CuriousTech/UT181A_WiFi/Arduino/jsonstring.h

// JSON string helper

class jsonString
{
public:
  jsonString(const char *pLabel = NULL)
  {
    m_cnt = 0;
    s = String("{");
    if(pLabel)
    {
      s += "\"cmd\":\"";
      s += pLabel, s += "\",";
    }
  }
        
  String Close(void)
  {
    s += "}";
    return s;
  }

  void Var(const char *key, int iVal)
  {
    if(m_cnt) s += ",";
    s += "\"";
    s += key;
    s += "\":";
    s += iVal;
    m_cnt++;
  }

  void Var(const char *key, uint32_t iVal)
  {
    if(m_cnt) s += ",";
    s += "\"";
    s += key;
    s += "\":";
    s += iVal;
    m_cnt++;
  }

  void Var(const char *key, long int iVal)
  {
    if(m_cnt) s += ",";
    s += "\"";
    s += key;
    s += "\":";
    s += iVal;
    m_cnt++;
  }

  void Var(const char *key, float fVal)
  {
    if(m_cnt) s += ",";
    s += "\"";
    s += key;
    s += "\":";
    s += fVal;
    m_cnt++;
  }
  
  void Var(const char *key, bool bVal)
  {
    if(m_cnt) s += ",";
    s += "\"";
    s += key;
    s += "\":";
    s += bVal ? 1:0;
    m_cnt++;
  }
  
  void Var(const char *key, const char *sVal)
  {
    if(m_cnt) s += ",";
    s += "\"";
    s += key;
    s += "\":\"";
    s += sVal;
    s += "\"";
    m_cnt++;
  }

  void Var(const char *key, String sVal)
  {
    if(m_cnt) s += ",";
    s += "\"";
    s += key;
    s += "\":\"";
    s += sVal;
    s += "\"";
    m_cnt++;
  }

  void VarNoQ(const char *key, String sVal)
  {
    if(m_cnt) s += ",";
    s += "\"";
    s += key;
    s += "\":";
    s += sVal;
    m_cnt++;
  }

  void Array(const char *key, uint16_t iVal[], int n)
  {
    if(m_cnt) s += ",";
    s += "\"";
    s += key;
    s += "\":[";
    for(int i = 0; i < n; i++)
    {
      if(i) s += ",";
      s += iVal[i];
    }
    s += "]";
    m_cnt++;
  }

  void Array(const char *key, const char **szVal)
  {
    if(m_cnt) s += ",";
    s += "\"";
    s += key;
    s += "\":[";
    for(int i = 0; szVal[i]; i++)
    {
      if(i) s += ",";
      s += "[\"";
      s += szVal[i];
      s += "\"]";
    }
    s += "]";
    m_cnt++;
  }

  void Array(const char *key, String sVal[])
  {
    if(m_cnt) s += ",";
    s += "\"";
    s += key;
    s += "\":[";
    for(int i = 0; sVal[i].length(); i++)
    {
      if(i) s += ",";
      s += "[\"";
      s += sVal[i];
      s += "\"]";
    }
    s += "]";
    m_cnt++;
  }

protected:
  String s;
  int m_cnt;
};
